alfredopalhares/freeems-box/src/BOLTS/common/version.scad

function BOLTS_version() = "unstable";
function BOLTS_date() = [2013,10,30];
