alfredopalhares/freeems-box/src/BOLTS/tables/din11850range2_table.scad

/* Generated by BOLTS, do not modify */
/* Copyright by: Johannes Reinhardt <jreinhardt@ist-dein-freund.de> */
/* MIT <http://opensource.org/licenses/MIT> */
function din11850range2_table_0(key) = 
//id, od
key == "150" ? [150.0, 154.0] : 
key == "200" ? [200.0, 204.0] : 
key == "20" ? [20.0, 23.0] : 
key == "10" ? [10.0, 13.0] : 
key == "25" ? [26.0, 29.0] : 
key == "32" ? [32.0, 35.0] : 
key == "50" ? [50.0, 53.0] : 
key == "40" ? [38.0, 41.0] : 
key == "65" ? [66.0, 70.0] : 
key == "6" ? [6.0, 8.0] : 
key == "15" ? [16.0, 19.0] : 
key == "100" ? [100.0, 104.0] : 
key == "80" ? [81.0, 85.0] : 
key == "125" ? [125.0, 129.0] : 
key == "8" ? [8.0, 10.0] : 
"Error";
