alfredopalhares/freeems-box/src/BOLTS/tables/heavydutyplainwasher_table.scad

/* Generated by BOLTS, do not modify */
/* Copyright by: Johannes Reinhardt <jreinhardt@ist-dein-freund.de> */
/* LGPL 2.1+ <http://www.gnu.org/licenses/lgpl-2.1> */
function heavydutyplainwasher_table_0(key) = 
//d1, d2, s
key == "M10" ? [10.5, 25.0, 4.0] : 
key == "M24" ? [25.0, 50.0, 10.0] : 
key == "M27" ? [28.0, 60.0, 10.0] : 
key == "M20" ? [21.0, 44.0, 8.0] : 
key == "M22" ? [23.0, 50.0, 8.0] : 
key == "M30" ? [31.0, 68.0, 10.0] : 
key == "M5" ? [5.3, 15.0, 2.0] : 
key == "M4" ? [4.3, 12.0, 1.6] : 
key == "M6" ? [6.4, 17.0, 3.0] : 
key == "M14" ? [15.0, 36.0, 6.0] : 
key == "M3" ? [3.2, 9.0, 1.0] : 
key == "M16" ? [17.0, 40.0, 6.0] : 
key == "M18" ? [19.0, 44.0, 8.0] : 
key == "M12" ? [13.0, 30.0, 6.0] : 
key == "M8" ? [8.4, 21.0, 4.0] : 
"Error";
