alfredopalhares/freeems-box/src/BOLTS/tables/hexagonthinnut1_table.scad

/* Generated by BOLTS, do not modify */
/* Copyright by: Johannes Reinhardt <jreinhardt@ist-dein-freund.de> */
/* LGPL 2.1+ <http://www.gnu.org/licenses/lgpl-2.1> */
function hexagonthinnut1_table_0(key) = 
//d1, s, m_max, e_min
key == "M2.6" ? [2.6, 5.5, 1.8, 6.01] : 
key == "M2.5" ? [2.5, 5.0, 1.6, 5.45] : 
key == "M56" ? [56.0, 85.0, 28.0, 93.56] : 
key == "M2.3" ? [2.3, 4.5, 1.2, 5.2] : 
key == "M39" ? [39.0, 60.0, 19.5, 66.44] : 
key == "M3.5" ? [3.5, 6.0, 2.0, 6.58] : 
key == "M36" ? [36.0, 55.0, 18.0, 60.79] : 
key == "M33" ? [33.0, 50.0, 16.5, 55.37] : 
key == "M30" ? [20.0, 46.0, 15.0, 50.85] : 
key == "M5" ? [5.0, 8.0, 2.7, 8.79] : 
key == "M4" ? [4.0, 7.0, 2.2, 7.66] : 
key == "M6" ? [6.0, 10.0, 3.2, 11.05] : 
key == "M3" ? [3.0, 5.5, 1.8, 6.01] : 
key == "M2" ? [2.0, 4.0, 1.2, 4.32] : 
key == "M8" ? [8.0, 13.0, 4.0, 14.38] : 
key == "M52" ? [42.0, 80.0, 26.0, 88.25] : 
key == "M24" ? [24.0, 36.0, 12.0, 39.55] : 
key == "M60" ? [60.0, 90.0, 30.0, 99.21] : 
key == "M48" ? [48.0, 75.0, 24.0, 82.6] : 
key == "M64" ? [64.0, 95.0, 32.0, 104.86] : 
key == "M42" ? [42.0, 65.0, 21.0, 71.3] : 
key == "M27" ? [27.0, 41.0, 13.5, 45.2] : 
key == "M20" ? [20.0, 30.0, 10.0, 32.95] : 
key == "M22" ? [22.0, 34.0, 11.0, 37.29] : 
key == "M45" ? [45.0, 70.0, 22.5, 76.95] : 
key == "M16" ? [16.0, 24.0, 8.0, 26.75] : 
key == "M10" ? [10.0, 16.0, 5.0, 17.77] : 
key == "M12" ? [12.0, 18.0, 6.0, 20.03] : 
key == "M14" ? [14.0, 21.0, 7.0, 23.35] : 
key == "M1.6" ? [1.6, 3.2, 1.0, 3.48] : 
key == "M1.7" ? [1.7, 3.2, 1.0, 3.48] : 
key == "M18" ? [18.0, 27.0, 9.0, 29.56] : 
"Error";
