alfredopalhares/freeems-box/src/BOLTS/tables/plainwasher1_table.scad

/* Generated by BOLTS, do not modify */
/* Copyright by: Johannes Reinhardt <jreinhardt@ist-dein-freund.de> */
/* LGPL 2.1+ <http://www.gnu.org/licenses/lgpl-2.1> */
function plainwasher1_table_0(key) = 
//d1, d2, s
key == "M2.6" ? [2.8, 7.0, 0.5] : 
key == "M2.5" ? [2.7, 6.0, 0.5] : 
key == "M56" ? [58.0, 105.0, 9.0] : 
key == "M2.3" ? [2.5, 6.0, 0.5] : 
key == "M2.2" ? [2.4, 6.0, 0.5] : 
key == "M39" ? [40.0, 72.0, 6.0] : 
key == "M3.5" ? [3.7, 8.0, 0.5] : 
key == "M36" ? [37.0, 66.0, 5.0] : 
key == "M33" ? [34.0, 60.0, 5.0] : 
key == "M30" ? [31.0, 56.0, 4.0] : 
key == "M72" ? [74.0, 125.0, 10.0] : 
key == "M4" ? [4.3, 9.0, 0.8] : 
key == "M7" ? [7.4, 14.0, 1.6] : 
key == "M6" ? [6.4, 12.0, 1.6] : 
key == "M1" ? [1.1, 3.0, 0.3] : 
key == "M3" ? [3.2, 7.0, 0.5] : 
key == "M2" ? [2.2, 5.0, 0.3] : 
key == "M8" ? [8.4, 16.0, 1.6] : 
key == "M76" ? [78.0, 135.0, 10.0] : 
key == "M85" ? [87.0, 145.0, 12.0] : 
key == "M80" ? [82.0, 140.0, 12.0] : 
key == "M42" ? [43.0, 78.0, 7.0] : 
key == "M60" ? [62.0, 110.0, 9.0] : 
key == "M48" ? [50.0, 92.0, 8.0] : 
key == "M64" ? [64.0, 115.0, 9.0] : 
key == "M24" ? [25.0, 44.0, 4.0] : 
key == "M27" ? [28.0, 50.0, 4.0] : 
key == "M20" ? [21.0, 37.0, 3.0] : 
key == "M22" ? [23.0, 39.0, 3.0] : 
key == "M45" ? [46.0, 85.0, 7.0] : 
key == "M16" ? [17.0, 30.0, 3.0] : 
key == "M5" ? [5.3, 10.0, 1.0] : 
key == "M100" ? [104.0, 175.0, 14.0] : 
key == "M52" ? [54.0, 98.0, 8.0] : 
key == "M90" ? [93.0, 160.0, 12.0] : 
key == "M68" ? [70.0, 120.0, 10.0] : 
key == "M10" ? [10.0, 20.0, 2.0] : 
key == "M1.2" ? [1.3, 3.5, 0.3] : 
key == "M12" ? [13.0, 24.0, 2.5] : 
key == "M1.4" ? [1.5, 4.0, 0.3] : 
key == "M14" ? [15.0, 28.0, 2.5] : 
key == "M1.6" ? [1.7, 4.0, 0.3] : 
key == "M1.7" ? [1.8, 4.5, 0.3] : 
key == "M18" ? [19.0, 34.0, 3.0] : 
"Error";
